Dioxgen/DIY-BW-Enlarger/Images/Durst M305.jpg

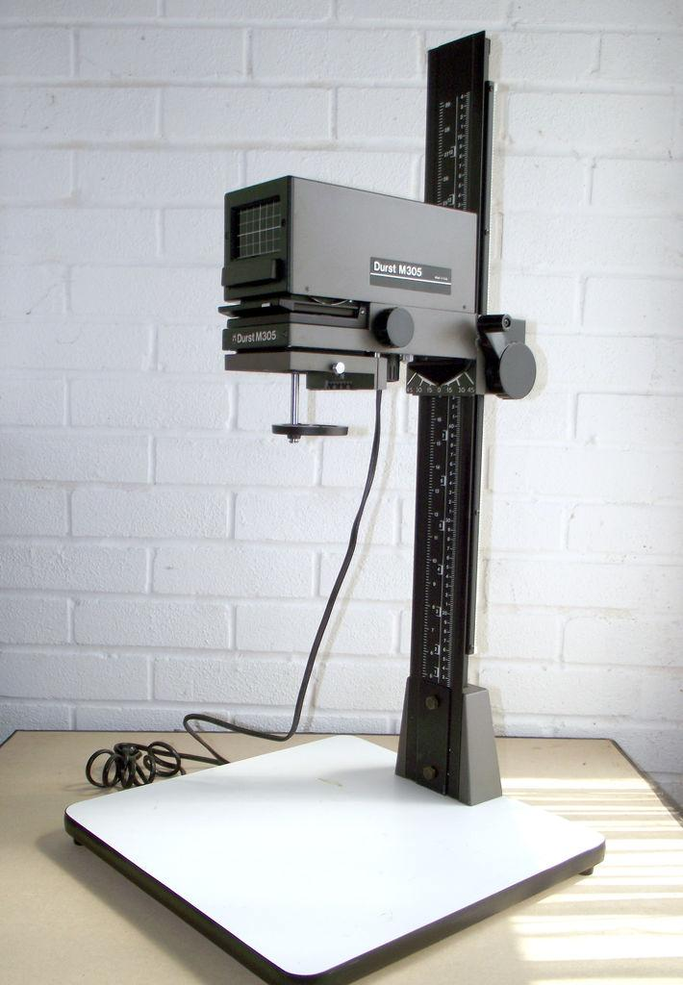
Images/Durst M305.jpg
